BoujeeEnjinia1701/thermacart/cad/drawings/TCT-DWG-001.pdf

CONCEPT, NOT FOR FABRICATION | ThermaCart · github.com/BoujeeEnjinia1701/thermacart

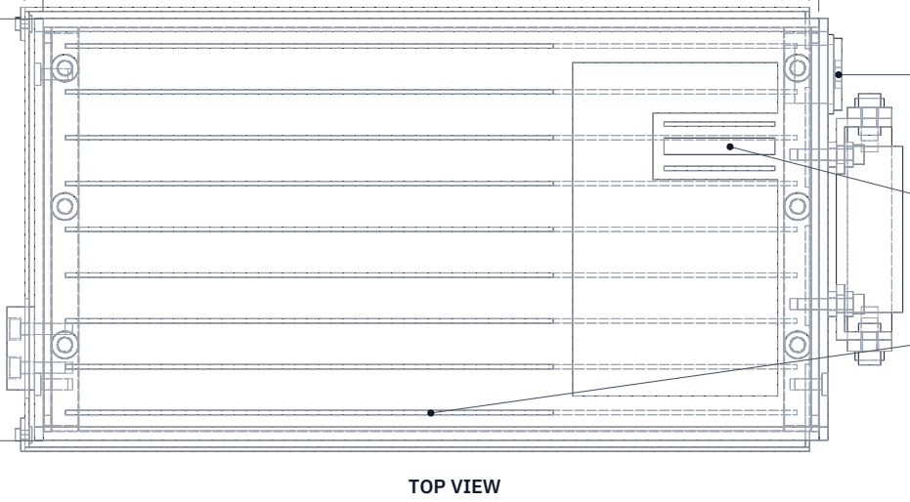
[picture p7: figure]
TOP VIEW

FRONT VIEW
Scale 1:2.5; looking at the front (along +Y)

Scale 1:2.5; looking down (along -Z)

RIGHT VIEW
Scale 1:2.5; looking at the right side (along -X)

323

160 65

323.4 overall (GN 1/3: 325)

63.5

FOLDING BAIL, STOWED

GRADE KEY

ADAPTER FRAME, KEYED STOP | 4 MM LIP

280 tube

283.2 frame

152.4

160.4 frame
MELT INDICATOR

G 1/2 FILL PORT

FINS, 9 TOP AND 9 BOTTOM

HANDLE END

ISOMETRIC VIEW
Not to scale; seen from the front right and above, about 30 deg elevation

MAIN DIMENSIONS AND INTERFACES (MM)
Shell 6 x 2 x 1/8 in tube, 280 long; inner 146.1 x 44.4 x 254.9 Inner volume 1.655 L; filled to 90 % as liquid at the grade limit
Fins 9 top, 9 bottom, 6.35 x 1.59 on 16.6 pitch
Caps: 3.175 flange, 3 spacer, 9.525 plug, bonded; FKM 2.5 cord
Six radial M5 button-head screws per cap on bonded seals; G 1/2 fill port Bail: 20 x 20 x 3 angles on 3 phenolic washers; finger gap 39 raised
Key tab 30 wide, 16 high, 2 x M4; centre Y: C5 -43, C25 +0, H70 +43, W0 -61 Frame 1.5 sheet, 283 x 160; key passes the stop slot (key + 3)
Frame lip 4 high, 3 past the seated fins; a wrong grade stops 8 short on it
Finish: shell, fins and caps etch-primed, matte black high-temp paint (e about 0.9) H70 label rule: from an oven use oven gloves or wait 12 min; pad charging preferred Sized in TCT-CAL-001; shown: C5 key and C5 frame
Third-angle; front view from -Y; handle end at +X
REV | DESCRIPTION | DATE | BY
P1 | Preliminary GA for TRL 3 (from cad/src/model.py) | 2026-09-25 | AC
P2 | Dark finish and H70 handling rule added (TCT-DDR-002) | 2026-09-25 | AC
P3 | Layout and labels tidied | 2026-09-25 | AC
P4 | Constructable design (TCT-DDR-003) | 2026-10-01 | AC
P5 | Frame lip and raised grip (TCT-DEC-001 item 1) | 2026-10-02 | AC
THERMACART | github.com/BoujeeEnjinia1701/thermacart

## General arrangement, TC-L in frame

DRAWING NO.
TCT-DWG-001

REV
P5

SHEET
1 of 1

SIZE

## ANSI B

SCALE
1:2.5

UNITS
mm
PROJECTION | DATE
2026-10-02

DRAWN
Amish Chadha

MATERIAL / NOTES
6063-T52 tube, 6061 caps, 5052 frame; FKM seals; matte black finish. PRELIMINARY, NOT FOR FABRICATION
Licensed CERN-OHL-S-2.0 · Design Molecule Lab · designmolecule.com | Generated from cad/src; do not edit by hand
