BoujeeEnjinia1701/thermacart/cad/drawings/TCT-DWG-106.pdf

BUILD PLAN SKETCH, PLAN NOT YET BUILT ThermaCart · github.com/BoujeeEnjinia1701/thermacart

FRONT VIEW
Scale 2:1; looking at the front (along +Y)

TOP VIEW
Scale 2:1; looking down (along -Z)

RIGHT VIEW
Scale 2:1; looking at the right side (along -X)

20

20 32

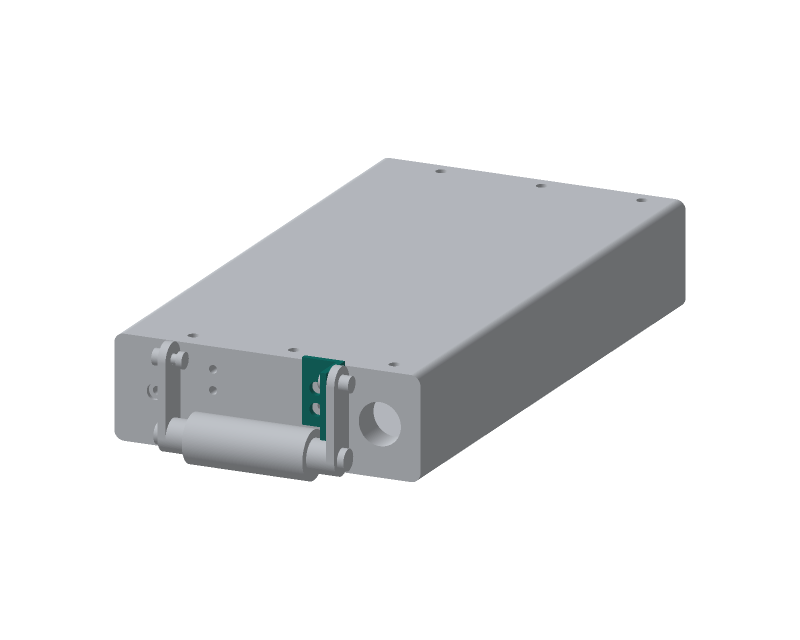
[picture p8: figure]

WHERE IT GOES
This part in colour, its neighbours in grey

HOW TO MAKE IT AND HOW IT FITS
Cut two 32 mm lengths of 20 x 20 x 3 angle; deburr.
Flat leg (goes on the cap): two 6.5 mm holes 13 mm from the outside of the upright leg, 8 and 18 mm up from the bottom end. The
bolts pass with 1.25 mm air all round: the bolt must not touch. Upright leg: one 5.2 mm pivot hole 12 mm out from the back of
the flat leg, 25.5 mm up from the bottom end.
Left and right are mirror images: drill them as a pair.
Fit: flat leg on two phenolic washers (9 x 4.5 x 3 mm) per bolt, 3 mm off the flange; bottom end 22 mm above the flange's bottom edge; upright legs outward, their outsides 40 mm each side of the centre line. M4 x 20 bolts with a 3 mm phenolic washer under each head, into the plug.
Check: no metal path from bolt to angle (meter: open circuit).
REV | DESCRIPTION | DATE | BY
P1 | Making sketch for the prototype build plan | 2026-10-01 | AC
P2 | Pivot hole moved up 1.5 mm (raised grip) | 2026-10-02 | AC
THERMACART | github.com/BoujeeEnjinia1701/thermacart

## ThermaCart lug angle (make 2, a left and a right): making sketch

DRAWING NO.
TCT-DWG-106

REV
P2

SHEET
1 of 1

SIZE

## ANSI B

SCALE
2:1

UNITS
mm
PROJECTION | DATE
2026-10-02

DRAWN
Amish Chadha

MATERIAL / NOTES
6063 equal angle 20 x 20 x 3 mm
Licensed CERN-OHL-S-2.0 · Design Molecule Lab · designmolecule.com | Generated from cad/src; do not edit by hand
