BoujeeEnjinia1701/thermacart/cad/drawings/TCT-DWG-107.pdf

BUILD PLAN SKETCH, PLAN NOT YET BUILT ThermaCart · github.com/BoujeeEnjinia1701/thermacart

FRONT VIEW
Scale 2:1; looking at the front (along +Y)

TOP VIEW
Scale 2:1; looking down (along -Z)

RIGHT VIEW
Scale 2:1; looking at the right side (along -X)

16

4 52

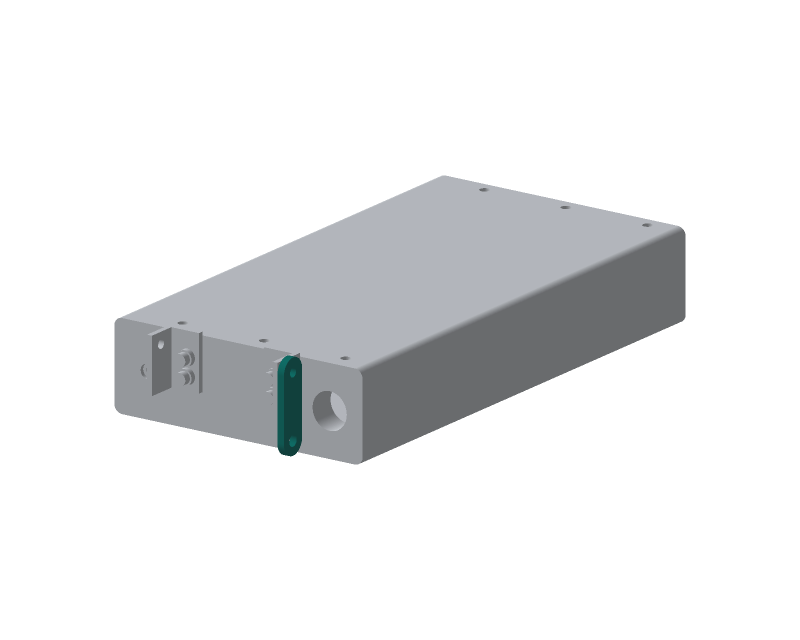
[picture p9: figure]

WHERE IT GOES
This part in colour, its neighbours in grey

HOW TO MAKE IT AND HOW IT FITS
Cut two 52 mm lengths of 16 x 4 mm flat bar.
Round both ends to an 8 mm radius (file to a scribed circle).
Two holes on the centre line, 8 mm from each end (36 mm apart): 5.2 mm at the top (pivot), 6.5 mm at the bottom (rod end).
Drill the two arms clamped together so the holes match.
Fit: the arm lies flat on the outside of the angle's upright leg;
a 5 mm stainless pin goes through both, head inside the angle, nyloc nut outside the arm, snug so the arm still swings.
The rod end butts on the arm's inside face; one M6 x 12 button-head screw through the arm into the rod.
Stowed, the arm hangs straight down; raised, the grip is 39 mm from the end face (room for fingers).
Check: hole centres 36 mm apart, within 0.5 mm.
REV | DESCRIPTION | DATE | BY
P1 | Making sketch for the prototype build plan | 2026-10-01 | AC
P2 | Arms 36 mm between holes (raised grip) | 2026-10-02 | AC
THERMACART | github.com/BoujeeEnjinia1701/thermacart

## ThermaCart bail arm (make 2): making sketch

DRAWING NO.
TCT-DWG-107

REV
P2

SHEET
1 of 1

SIZE

## ANSI B

SCALE
2:1

UNITS
mm
PROJECTION | DATE
2026-10-02

DRAWN
Amish Chadha

MATERIAL / NOTES
6060 flat bar 16 x 4 mm
Licensed CERN-OHL-S-2.0 · Design Molecule Lab · designmolecule.com | Generated from cad/src; do not edit by hand
