BoujeeEnjinia1701/thermacart/cad/drawings/TCT-DWG-108.pdf

BUILD PLAN SKETCH, PLAN NOT YET BUILT ThermaCart · github.com/BoujeeEnjinia1701/thermacart

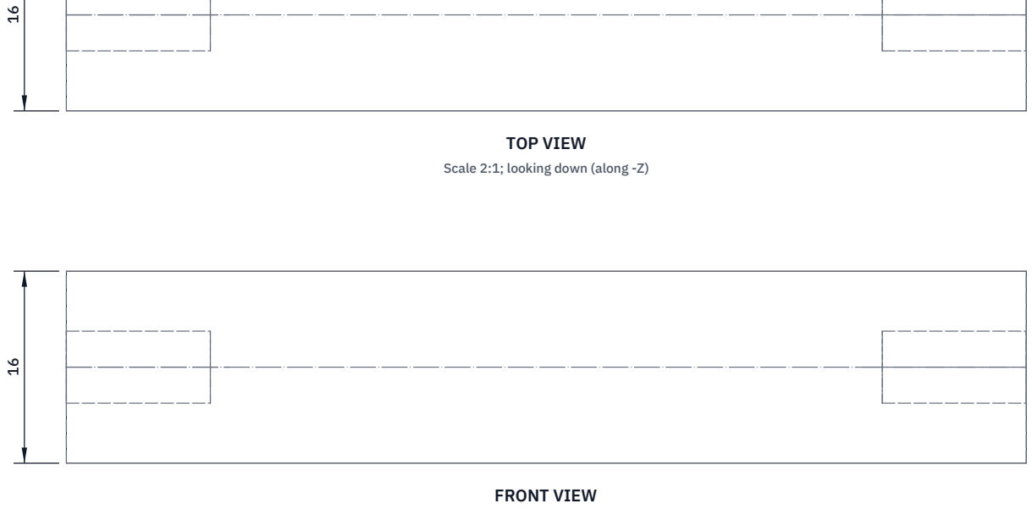
[picture p10: figure]
FRONT VIEW; TOP VIEW; Scale 2:1; looking down (along -Z)

Scale 2:1; looking at the front (along +Y)

RIGHT VIEW
Scale 2:1; looking at the right side (along -X)

80

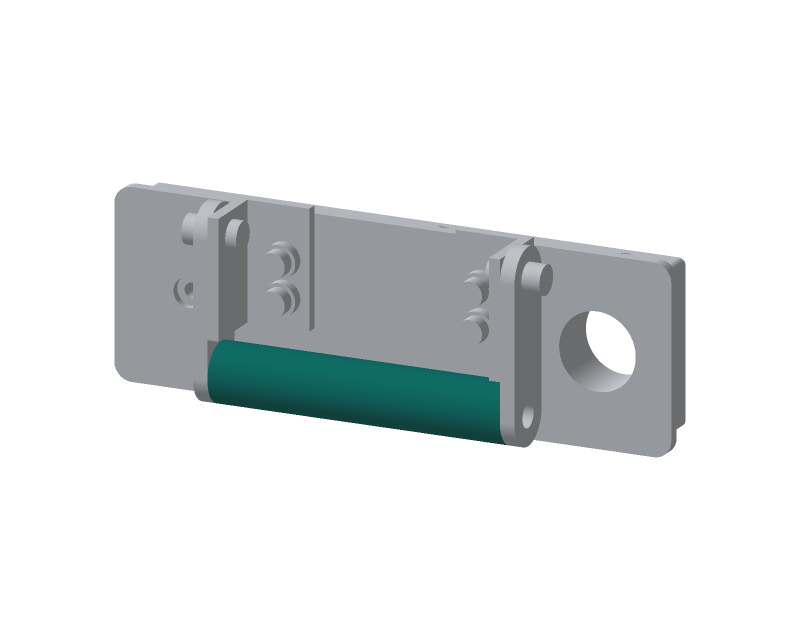
[picture p11: figure]

WHERE IT GOES
This part in colour, its neighbours in grey

HOW TO MAKE IT AND HOW IT FITS
Cut 80 mm of 16 mm round bar; face both ends square. Centre drill each end, drill 5 mm 14 deep and tap M6 12 deep (drill press with the bar upright in a V-block).
Break the edges 0.5 mm.
Slide the 60 mm silicone grip sleeve onto the middle (soapy water helps; let it dry).
Fit: between the two arms' inside faces, held by one M6 x 12 button-head screw through each arm, with medium threadlocker. Stowed, the rod hangs 11.5 mm above the tube's underside, 15 mm out from the end face; the grip clears the flange by 3 mm
and stays above the frame's lip.
Leave the rod bare: the bail is not painted.
Check: 80 mm long, within 0.3 mm, so the arms are not pulled in or pushed out.
REV | DESCRIPTION | DATE | BY
P1 | Making sketch for the prototype build plan | 2026-10-01 | AC
P2 | Rod hangs higher (raised grip) | 2026-10-02 | AC
THERMACART | github.com/BoujeeEnjinia1701/thermacart

## ThermaCart bail rod: making sketch

DRAWING NO.
TCT-DWG-108

REV
P2

SHEET
1 of 1

SIZE

## ANSI B

SCALE
2:1

UNITS
mm
PROJECTION | DATE
2026-10-02

DRAWN
Amish Chadha

MATERIAL / NOTES
6061 round bar 16 mm
Licensed CERN-OHL-S-2.0 · Design Molecule Lab · designmolecule.com | Generated from cad/src; do not edit by hand
