BoujeeEnjinia1701/thermacart/cad/drawings/TCT-DWG-110.pdf

BUILD PLAN SKETCH, PLAN NOT YET BUILT ThermaCart · github.com/BoujeeEnjinia1701/thermacart

FRONT VIEW
Scale 1:5; looking at the front (along +Y)

TOP VIEW
Scale 1:5; looking down (along -Z)

RIGHT VIEW
Scale 1:5; looking at the right side (along -X)

287

160 42

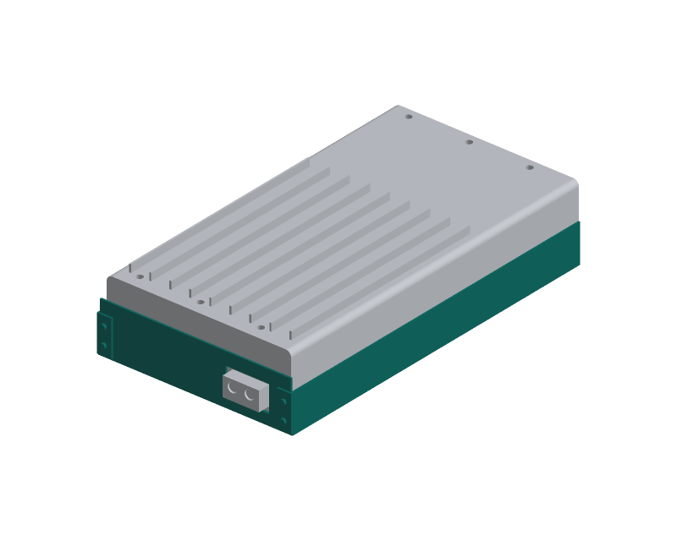
[picture p12: figure]

WHERE IT GOES
This part in colour, its neighbours in grey

HOW TO MAKE IT AND HOW IT FITS
Floor 283 x 160.4 mm; side walls 30 mm; end stop 40 mm. Mark one blank: floor in the middle, a wall on each long edge with a 12 mm tab at the stop end, and the stop on one short edge, 157.4 mm wide so it fits between the walls.
Cut the slot in the stop before bending: C5 36 x 22 mm, centred 43 mm toward the front, 7.35 to 29.35 mm above the floor's top. (C25 on the centre line, H70 43 mm toward the back.)
Drill 3 mm relief holes where bend lines cross.
Bend the stop up 90 degrees, then the walls (inside radius 1.5), then fold each tab round the outside of the stop.
Drill 3.3 mm through tab and stop, 6 mm in from the wall, 8 and 22 mm above the floor; rivet with heads inside the frame.
Lip: fold the open end of the floor up 4 mm; cut three
14 mm notches in it, centred 41.75 mm and 8.25 mm toward the front and 58.25 mm toward the back, for the screw heads. Stick the "C5 ONLY" decal on the stop beside the slot.
Check: inside width 157.4 mm; stop square to the floor.
REV | DESCRIPTION | DATE | BY
P1 | Making sketch for the prototype build plan | 2026-10-01 | AC
P2 | Lip at the open end and C5 ONLY decal | 2026-10-02 | AC
THERMACART | github.com/BoujeeEnjinia1701/thermacart

## ThermaCart adapter frame (C5 slot shown): making sketch

DRAWING NO.
TCT-DWG-110

REV
P2

SHEET
1 of 1

SIZE

## ANSI B

SCALE
1:5

UNITS
mm
PROJECTION | DATE
2026-10-02

DRAWN
Amish Chadha

MATERIAL / NOTES
5052-H32 aluminium sheet 1.5 mm; 3.2 mm blind rivets
Licensed CERN-OHL-S-2.0 · Design Molecule Lab · designmolecule.com | Generated from cad/src; do not edit by hand
