BoujeeEnjinia1701/thermacart/cad/drawings/TCT-DWG-101.pdf

BUILD PLAN SKETCH, PLAN NOT YET BUILT ThermaCart · github.com/BoujeeEnjinia1701/thermacart

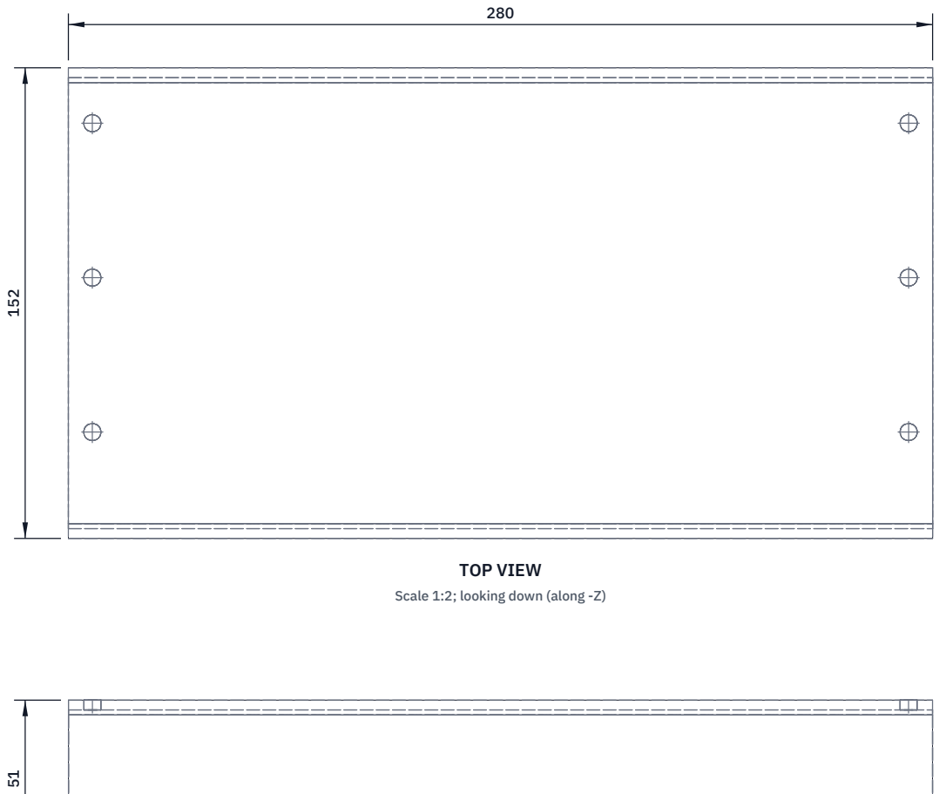
[picture p47: figure]
TOP VIEW; Scale 1:2; looking down (along -Z)

FRONT VIEW
Scale 1:2; looking at the front (along +Y)

RIGHT VIEW
Scale 1:2; looking at the right side (along -X)

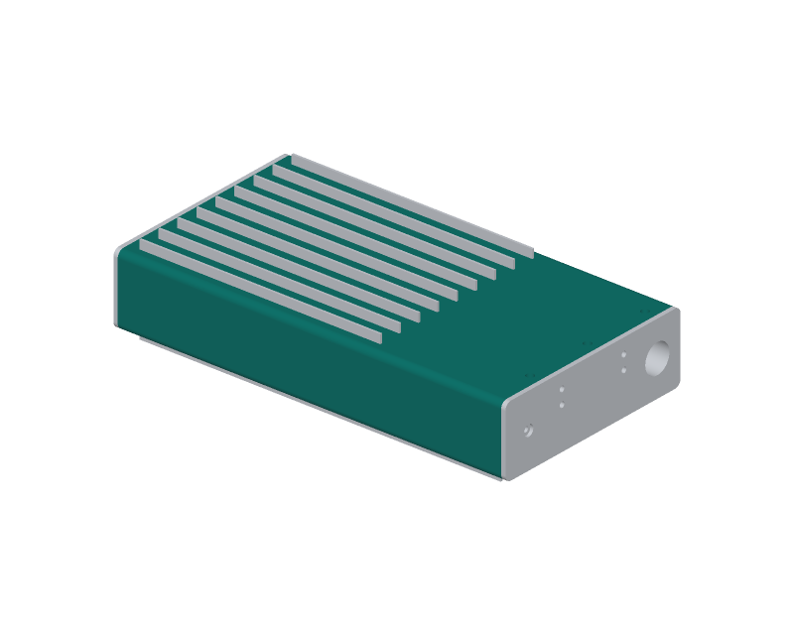
[picture p48: figure]

WHERE IT GOES
This part in colour, its neighbours in grey

HOW TO MAKE IT AND HOW IT FITS
Cut 280 mm long; square both ends to the side faces and file them flat. The cap flanges seat on these end faces.
File a 1 mm x 45 degree lead-in chamfer round the inside of each end, so the O-ring slides in without being cut.
Measure the bore at both ends (about 146.05 x 44.45 mm) and write it down: the cap plates are cut to it.
Radial screw holes: twelve 5.5 mm, 7.76 mm in from each end, through the top and the bottom wall, at 34.45, 84.45 and 134.45 mm from the front face (between the fins).
Drill them 4.2 mm first with the caps in place (see the caps). Deburr every edge and hole inside and out; clean, etch-prime the outside (not the bore) before the fins are bonded.
Check: the bore is clean and round-cornered; ends square.
REV | DESCRIPTION | DATE | BY
P1 | Making sketch for the prototype build plan | 2026-10-01 | AC
THERMACART | github.com/BoujeeEnjinia1701/thermacart

## ThermaCart shell tube: making sketch

DRAWING NO.
TCT-DWG-101

REV
P1

SHEET
1 of 1

SIZE

## ANSI B

SCALE
1:2

UNITS
mm
PROJECTION | DATE
2026-10-01

DRAWN
Amish Chadha

MATERIAL / NOTES
6063-T52 rectangular tube 6 x 2 x 1/8 in (152.4 x 50.8 x 3.175 mm)
Licensed CERN-OHL-S-2.0 · Design Molecule Lab · designmolecule.com | Generated from cad/src; do not edit by hand
