BoujeeEnjinia1701/thermacart/cad/drawings/TCT-DWG-102.pdf

BUILD PLAN SKETCH, PLAN NOT YET BUILT ThermaCart · github.com/BoujeeEnjinia1701/thermacart

FRONT VIEW
Scale 1:2; looking at the front (along +Y)

TOP VIEW
Scale 1:2; looking down (along -Z)

RIGHT VIEW
Scale 1:2; looking at the right side (along -X)

264

2 26

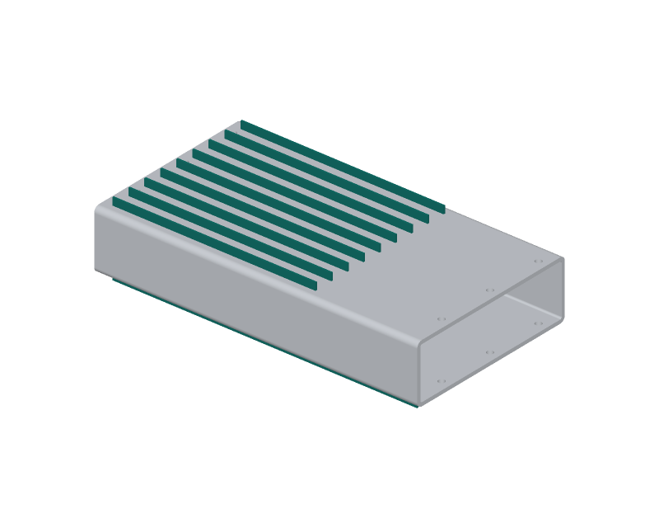
[picture p49: figure]

WHERE IT GOES
This part in colour, its neighbours in grey

HOW TO MAKE IT AND HOW IT FITS
Cut nine bottom fins 264 mm and nine top fins 176 mm long (two 3.66 m bars also give the two 40 mm indicator guards). Deburr; keep the long edges straight (roll them on a flat plate). Each fin stands on edge, 6.35 mm tall, on 16.55 mm centres; the outer fins are 10 mm in from the side faces.
Bottom fins start 8 mm in from each tube end.
Top fins start 8 mm in from the key end and stop 96 mm
short of the handle end, leaving the label band clear.
Bond with the 120 degree C epoxy: a thin bead under the edge and a fillet down each side. Hold them upright in a slotted comb
(a wooden strip sawn at the fin pitch) while the epoxy cures. Check: every fin upright, none touching a screw hole.
REV | DESCRIPTION | DATE | BY
P1 | Making sketch for the prototype build plan | 2026-10-01 | AC
THERMACART | github.com/BoujeeEnjinia1701/thermacart

## ThermaCart fins (make 9 long and 9 short): making sketch

DRAWING NO.
TCT-DWG-102

REV
P1

SHEET
1 of 1

SIZE

## ANSI B

SCALE
1:2

UNITS
mm
PROJECTION | DATE
2026-10-01

DRAWN
Amish Chadha

MATERIAL / NOTES
6063 flat bar 6.35 x 1.59 mm (1/4 x 1/16 in)
Licensed CERN-OHL-S-2.0 · Design Molecule Lab · designmolecule.com | Generated from cad/src; do not edit by hand
