BoujeeEnjinia1701/thermacart/cad/drawings/TCT-DWG-103.pdf

BUILD PLAN SKETCH, PLAN NOT YET BUILT ThermaCart · github.com/BoujeeEnjinia1701/thermacart

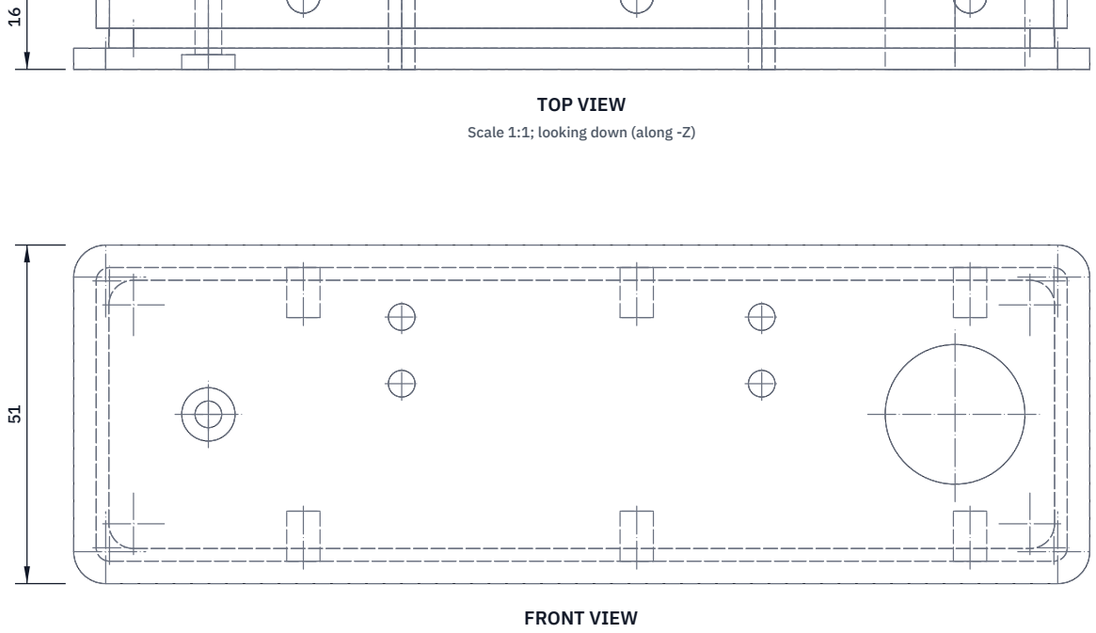
[picture p50: figure]
FRONT VIEW; TOP VIEW; Scale 1:1; looking down (along -Z)

Scale 1:1; looking at the front (along +Y)

RIGHT VIEW
Scale 1:1; looking at the right side (along -X)

152

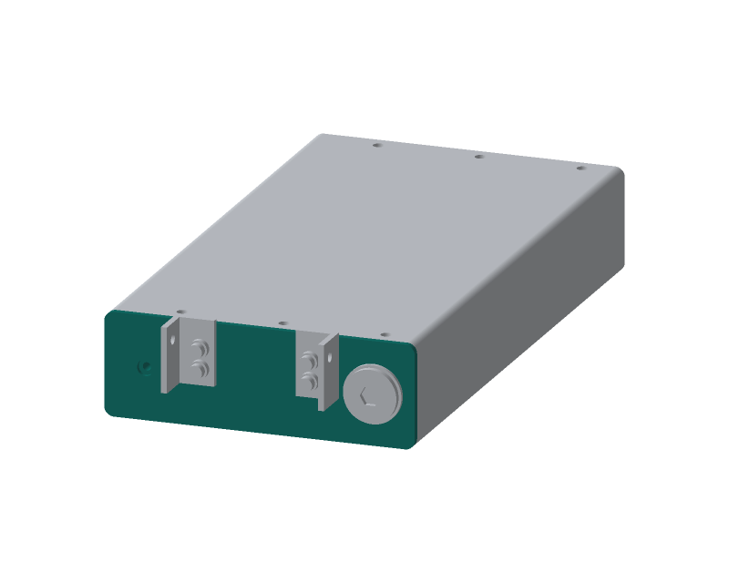
[picture p51: figure]

WHERE IT GOES
This part in colour, its neighbours in grey

HOW TO MAKE IT AND HOW IT FITS
Three plates, bonded face to face with the epoxy, then drilled. Flange 3.175 mm: 152.4 x 50.8, 4.8 mm corners (the tube's outside). Spacer 3 mm: the measured bore less 4.2 mm each way
(about 141.85 x 40.25), 3.7 mm corners. The O-ring goes round it. Plug 9.525 mm: the bore less 0.4 mm (about 145.65 x 44.05), 2 mm corners. Centre spacer and plug on the flange; bond and clamp. Seen from outside, handle end; sizes from the centre line, heights from the flange's bottom edge (layout picture in the plan):
fill port G 1/2 at 56 toward the back, 25.4 up, tapped through; lug bolts M4 at 27 each side, 30 and 40 up; one M4 countersunk stack screw at 56 toward the front, 25.4 up. All M4 holes 4.5 through flange and spacer, tapped 7.5 deep into the plug only. Radial holes: tap M5 7.5 deep into the plug edges (with the tube). Check: the stack slides into the tube without the O-ring.
REV | DESCRIPTION | DATE | BY
P1 | Making sketch for the prototype build plan | 2026-10-01 | AC
THERMACART | github.com/BoujeeEnjinia1701/thermacart

## ThermaCart handle-end cap stack (flange, spacer, plug): making sketch

DRAWING NO.
TCT-DWG-103

REV
P1

SHEET
1 of 1

SIZE

## ANSI B

SCALE
1:1

UNITS
mm
PROJECTION | DATE
2026-10-01

DRAWN
Amish Chadha

MATERIAL / NOTES
6061 plate 3.175, 3 and 9.525 mm; structural epoxy
Licensed CERN-OHL-S-2.0 · Design Molecule Lab · designmolecule.com | Generated from cad/src; do not edit by hand
