BoujeeEnjinia1701/thermacart/cad/drawings/TCT-DWG-104.pdf

BUILD PLAN SKETCH, PLAN NOT YET BUILT ThermaCart · github.com/BoujeeEnjinia1701/thermacart

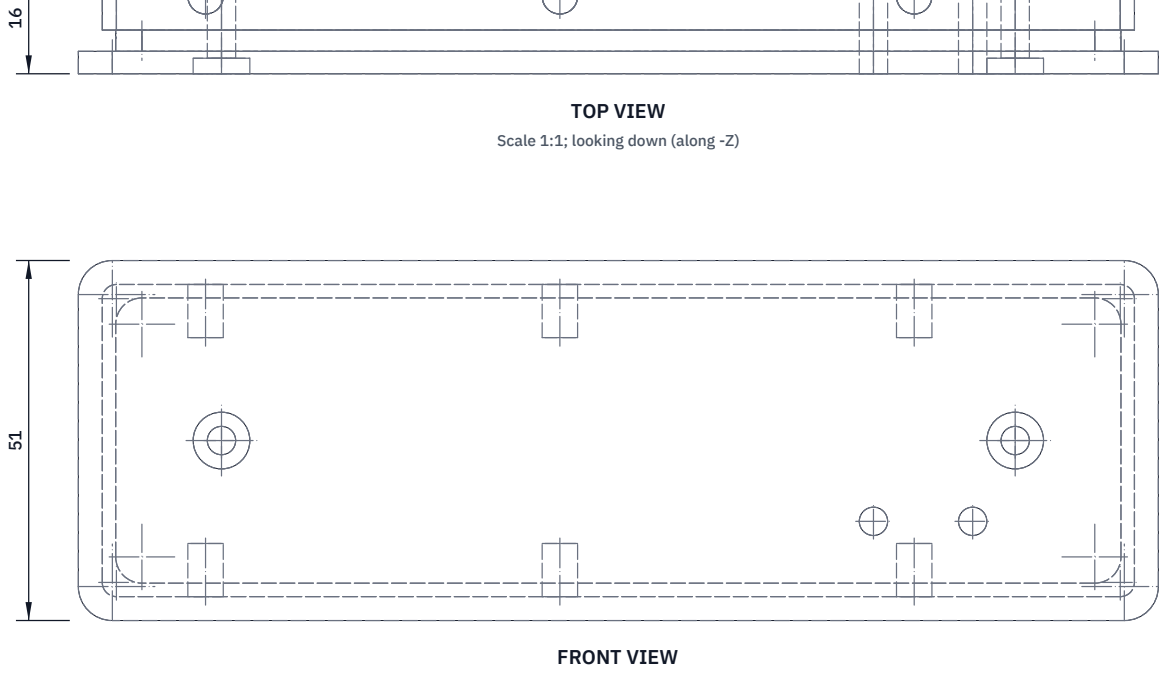
[picture p52: figure]
FRONT VIEW; TOP VIEW; Scale 1:1; looking down (along -Z)

Scale 1:1; looking at the front (along +Y)

RIGHT VIEW
Scale 1:1; looking at the right side (along -X)

152

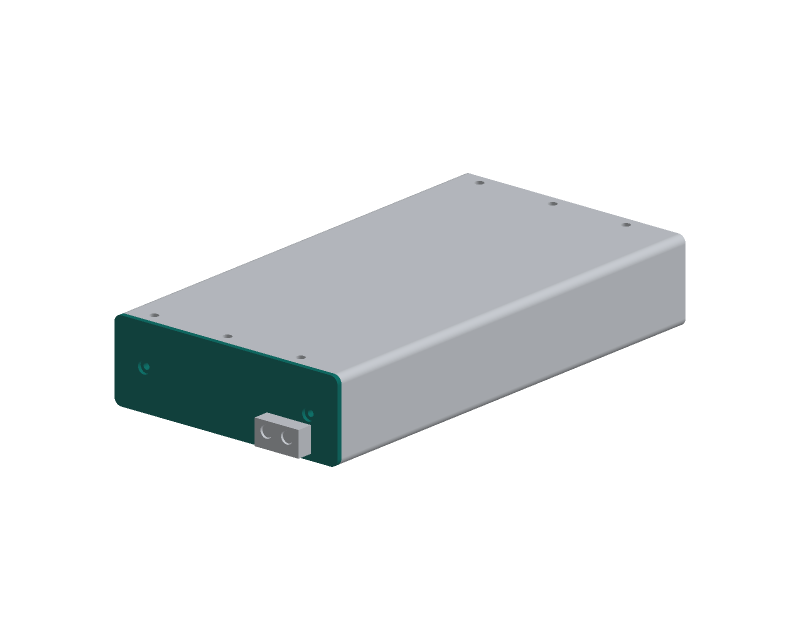
[picture p53: figure]

WHERE IT GOES
This part in colour, its neighbours in grey

HOW TO MAKE IT AND HOW IT FITS
Same three plates as the handle end, cut and bonded the same way. Seen from outside, key end; sizes from the centre line, heights
from the flange's bottom edge:
two M4 countersunk stack screws at 56 each side, 25.4 up;
two M4 key tab screws 7 each side of the key centre, 14 up.
C5 key centre: 43 toward the front (C25 0, H70 43 toward the back). M4 holes: 4.5 through flange and spacer, tapped 7.5 deep in
the plug, never through it (the plug's inner face is wet).
No fill port at this end.
Radial holes: with the stack in the tube (no O-ring yet), drill
4.2 mm through each tube hole into the plug edge, 7.5 deep; take the stack out, tap M5, open the tube holes to 5.5 mm.
Prime and paint the flange's outer face only.
Check: flange sits flat on the tube end all round.
REV | DESCRIPTION | DATE | BY
P1 | Making sketch for the prototype build plan | 2026-10-01 | AC
THERMACART | github.com/BoujeeEnjinia1701/thermacart

## ThermaCart key-end cap stack (flange, spacer, plug): making sketch

DRAWING NO.
TCT-DWG-104

REV
P1

SHEET
1 of 1

SIZE

## ANSI B

SCALE
1:1

UNITS
mm
PROJECTION | DATE
2026-10-01

DRAWN
Amish Chadha

MATERIAL / NOTES
6061 plate 3.175, 3 and 9.525 mm; structural epoxy
Licensed CERN-OHL-S-2.0 · Design Molecule Lab · designmolecule.com | Generated from cad/src; do not edit by hand
