BoujeeEnjinia1701/thermacart/cad/drawings/TCT-DWG-105.pdf

BUILD PLAN SKETCH, PLAN NOT YET BUILT ThermaCart · github.com/BoujeeEnjinia1701/thermacart

FRONT VIEW
Scale 2:1; looking at the front (along +Y)

TOP VIEW
Scale 2:1; looking down (along -Z)

RIGHT VIEW
Scale 2:1; looking at the right side (along -X)

10

30 16

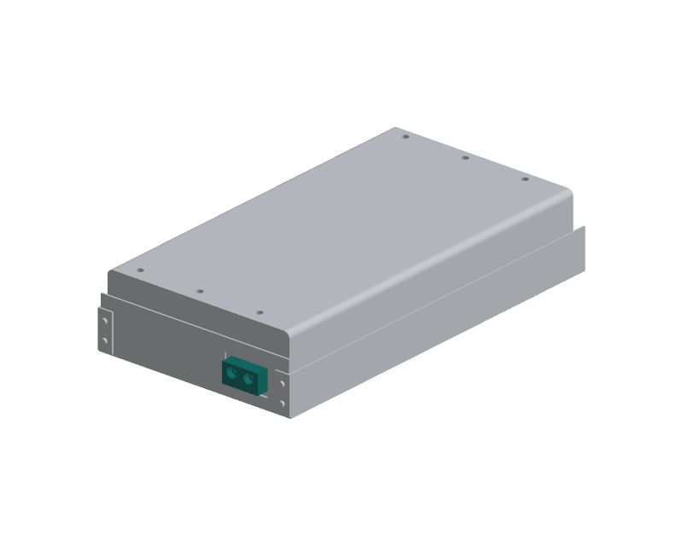
[picture p54: figure]

WHERE IT GOES
This part in colour, its neighbours in grey

HOW TO MAKE IT AND HOW IT FITS
Cut 16 mm off 30 x 10 mm flat bar: 30 wide, 16 tall, 10 deep.
Two 4.5 mm holes through the 10 mm depth, 8 mm in from each end (14 mm apart), 10 mm up from the bottom face.
Counterbore both from the front face 8 mm across, 5 mm deep, so the M4 x 16 socket cap screw heads sit below the face.
Break the front edges by 1 mm so it finds the slot easily.
Fit: back face flat on the key-end flange, bottom 4 mm above the flange's bottom edge, centre at the grade position:
C5 43 mm toward the front, C25 on the centre line,
H70 43 mm toward the back.
Leave it bare aluminium; stamp the grade on its top face. Check: 3 mm clear of the frame slot all round when seated.
REV | DESCRIPTION | DATE | BY
P1 | Making sketch for the prototype build plan | 2026-10-01 | AC
THERMACART | github.com/BoujeeEnjinia1701/thermacart

## ThermaCart key tab (C5 shown): making sketch

DRAWING NO.
TCT-DWG-105

REV
P1

SHEET
1 of 1

SIZE

## ANSI B

SCALE
2:1

UNITS
mm
PROJECTION | DATE
2026-10-01

DRAWN
Amish Chadha

MATERIAL / NOTES
6061 flat bar 30 x 10 mm
Licensed CERN-OHL-S-2.0 · Design Molecule Lab · designmolecule.com | Generated from cad/src; do not edit by hand
