BoujeeEnjinia1701/thermacart/cad/drawings/TCT-DWG-109.pdf

BUILD PLAN SKETCH, PLAN NOT YET BUILT ThermaCart · github.com/BoujeeEnjinia1701/thermacart

FRONT VIEW
Scale 2:1; looking at the front (along +Y)

TOP VIEW
Scale 2:1; looking down (along -Z)

RIGHT VIEW
Scale 2:1; looking at the right side (along -X)

40

18 6

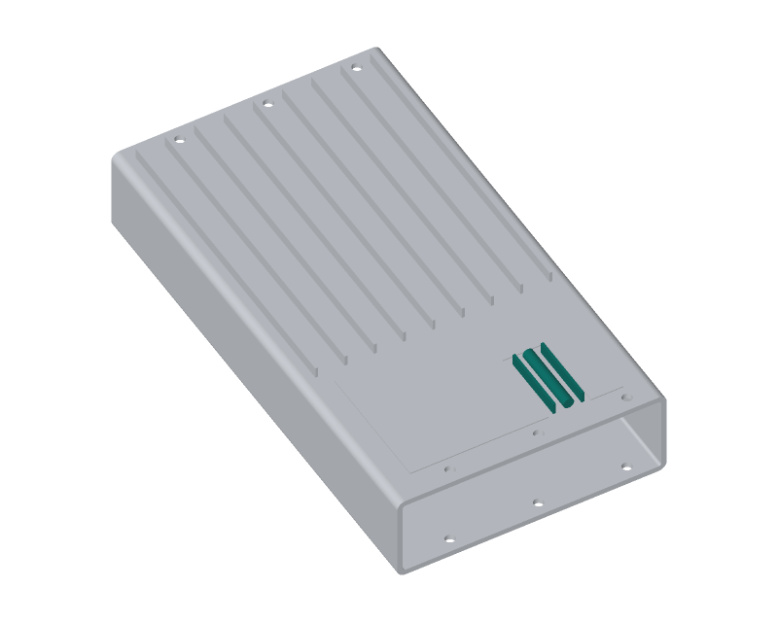
[picture p55: figure]

WHERE IT GOES
This part in colour, its neighbours in grey

HOW TO MAKE IT AND HOW IT FITS
Indicator: cut 40 mm of clear polycarbonate tube, 6 mm outside, 4 mm bore. Seal one end with a 3 mm plug of the epoxy; cure. Warm the grade's PCM just above its melting point and fill the tube with a syringe, leaving a 2 mm bubble; seal the other end with 3 mm of epoxy. Solid PCM is white, liquid PCM is clear. Guards: two 40 mm lengths of the fin bar.
Fit: bond the indicator to the painted top with the epoxy, along the cartridge, 30 mm toward the back from the centre line, between 16 and 56 mm from the handle end of the tube. Bond a guard on edge 8 mm each side of it; the guards are as tall as the fins and take knocks.
The label is notched round them.
Check: no PCM weeps at the plugs when warmed by hand.
REV | DESCRIPTION | DATE | BY
P1 | Making sketch for the prototype build plan | 2026-10-01 | AC
THERMACART | github.com/BoujeeEnjinia1701/thermacart

## ThermaCart melt indicator and guards: making sketch

DRAWING NO.
TCT-DWG-109

REV
P1

SHEET
1 of 1

SIZE

## ANSI B

SCALE
2:1

UNITS
mm
PROJECTION | DATE
2026-10-01

DRAWN
Amish Chadha

MATERIAL / NOTES
Clear polycarbonate tube 6 x 4 mm; fin bar 6.35 x 1.59 mm
Licensed CERN-OHL-S-2.0 · Design Molecule Lab · designmolecule.com | Generated from cad/src; do not edit by hand
