BoujeeEnjinia1701/thermacart/cad/drawings/TCT-DWG-001.png

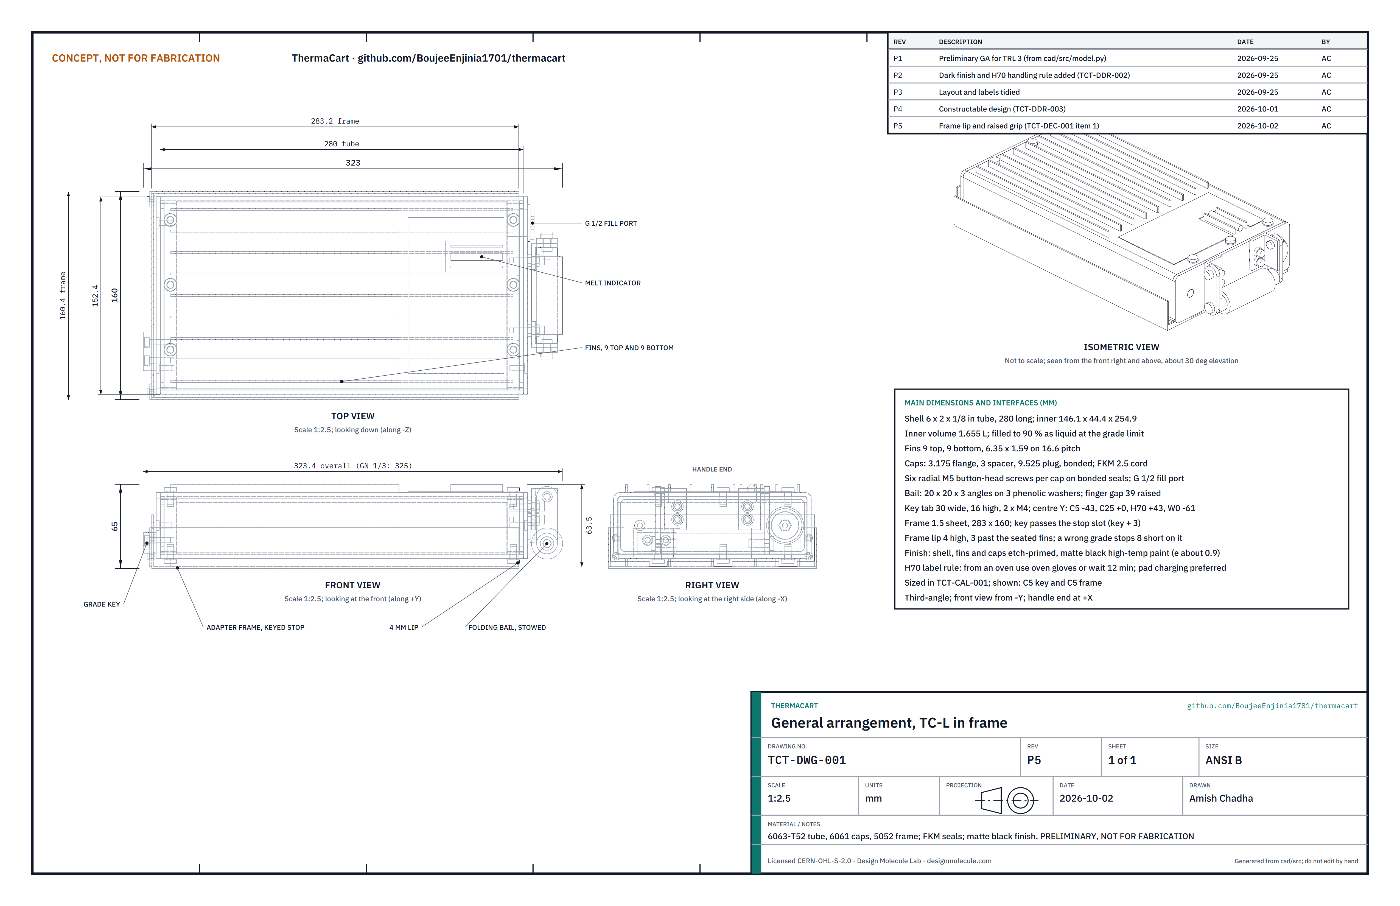
cad/drawings/TCT-DWG-001.png
