BoujeeEnjinia1701/thermacart/media/card.png

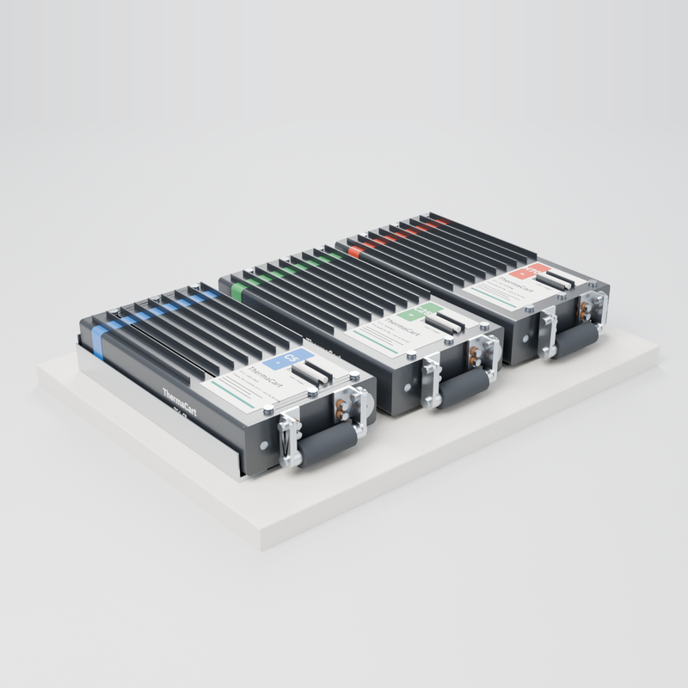
media/card.png
