BoujeeEnjinia1701/thermacart/media/render-detail.png

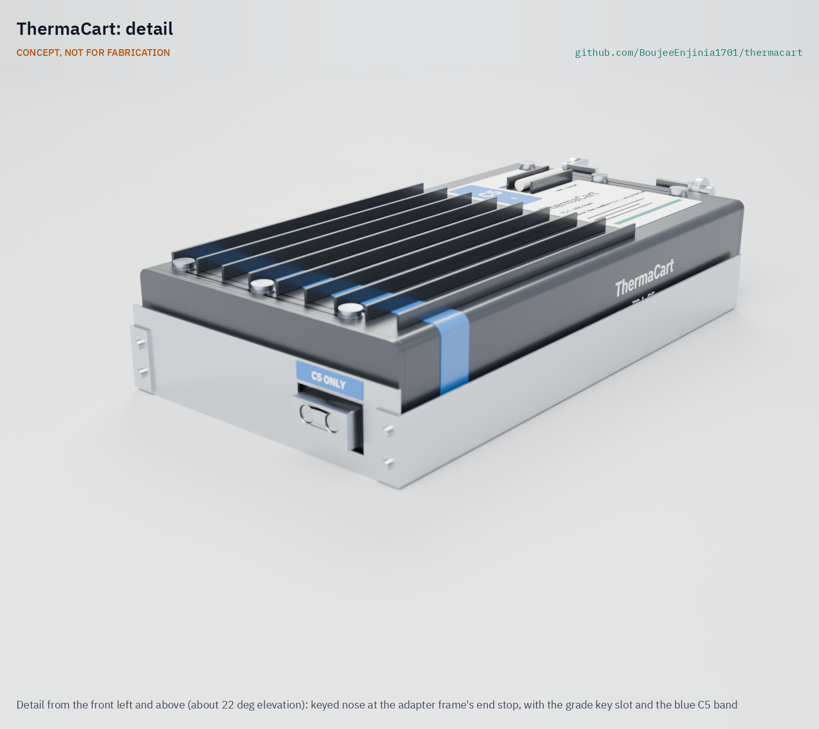
media/render-detail.png
