BoujeeEnjinia1701/thermacart/media/render-exploded.png

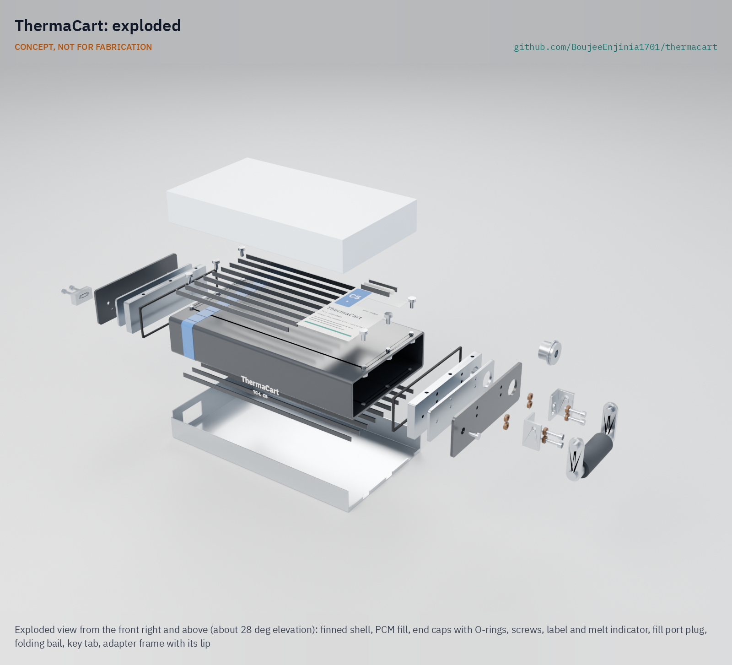
media/render-exploded.png
