BoujeeEnjinia1701/thermacart/media/social-preview.png

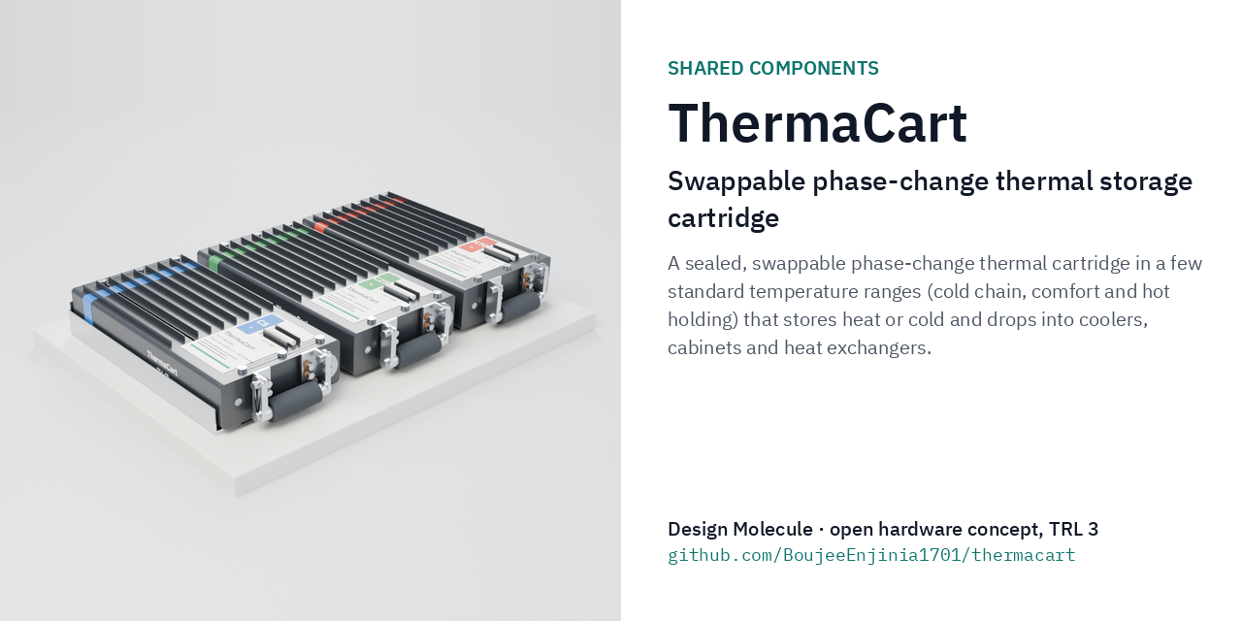
media/social-preview.png
